morganwang7777-ux/Morgan-s-Metronome-v1.0/images/3d-bottom.png

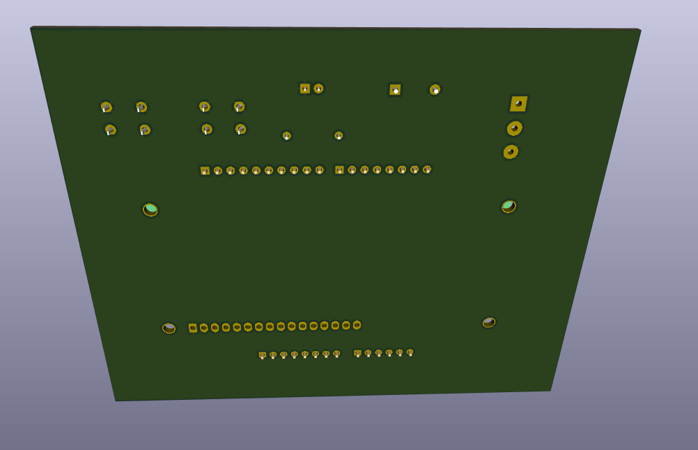
images/3d-bottom.png
